Vateva/esp32-c3-digital-dice/include/welcome_bitmap.h

#ifndef WELCOME_BITMAP_H
#define WELCOME_BITMAP_H

#include <pgmspace.h>
// 'welcome_image_dice', 128x16px
const unsigned char welcome_image_dice[] PROGMEM = {
	0x00, 0x00, 0x00, 0x00, 0x00, 0x00, 0x00, 0x00, 0x00, 0x00, 0x00, 0x00, 0x00, 0x00, 0x00, 0x00, 
	0x1f, 0xfe, 0x00, 0x7f, 0xf8, 0x01, 0xff, 0xe0, 0x07, 0xff, 0x80, 0x1f, 0xfe, 0x00, 0x7f, 0xf8, 
	0x3f, 0xff, 0x00, 0xff, 0xfc, 0x03, 0xff, 0xf0, 0x0f, 0xff, 0xc0, 0x3f, 0xff, 0x00, 0xff, 0xfc, 
	0x3f, 0xff, 0x00, 0xff, 0xfc, 0x03, 0xff, 0xf0, 0x0f, 0xff, 0xc0, 0x3f, 0xff, 0x00, 0xff, 0xfc, 
	0x3f, 0xff, 0x00, 0xe7, 0xfc, 0x03, 0x9f, 0xf0, 0x0e, 0x79, 0xc0, 0x39, 0xe7, 0x00, 0xe7, 0x9c, 
	0x3f, 0xff, 0x00, 0xe7, 0xfc, 0x03, 0x9f, 0xf0, 0x0e, 0x79, 0xc0, 0x39, 0xe7, 0x00, 0xe7, 0x9c, 
	0x3f, 0xff, 0x00, 0xff, 0xfc, 0x03, 0xff, 0xf0, 0x0f, 0xff, 0xc0, 0x3f, 0xff, 0x00, 0xff, 0xfc, 
	0x3f, 0x3f, 0x00, 0xff, 0xfc, 0x03, 0xf3, 0xf0, 0x0f, 0xff, 0xc0, 0x3f, 0x3f, 0x00, 0xe7, 0x9c, 
	0x3f, 0x3f, 0x00, 0xff, 0xfc, 0x03, 0xf3, 0xf0, 0x0f, 0xff, 0xc0, 0x3f, 0x3f, 0x00, 0xe7, 0x9c, 
	0x3f, 0xff, 0x00, 0xff, 0xfc, 0x03, 0xff, 0xf0, 0x0f, 0xff, 0xc0, 0x3f, 0xff, 0x00, 0xff, 0xfc, 
	0x3f, 0xff, 0x00, 0xff, 0x9c, 0x03, 0xfe, 0x70, 0x0e, 0x79, 0xc0, 0x39, 0xe7, 0x00, 0xe7, 0x9c, 
	0x3f, 0xff, 0x00, 0xff, 0x9c, 0x03, 0xfe, 0x70, 0x0e, 0x79, 0xc0, 0x39, 0xe7, 0x00, 0xe7, 0x9c, 
	0x3f, 0xff, 0x00, 0xff, 0xfc, 0x03, 0xff, 0xf0, 0x0f, 0xff, 0xc0, 0x3f, 0xff, 0x00, 0xff, 0xfc, 
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
	greyhound0,
	greyhound1,
	greyhound2
};
// Array of all bitmaps for convenience. (Total bytes used to store images in PROGMEM = 272)
const int welcome_image_dice_allArray_LEN = 1;
const unsigned char* welcome_image_dice_allArray[1] = {
	welcome_image_dice
};


#endif
