Vateva/esp32-c3-digital-dice/include/d10_bitmaps_32.h

#ifndef D10_BITMAPS_32_H
#define D10_BITMAPS_32_H

#include <pgmspace.h>
// 'd10_32_0', 32x32px
const unsigned char d10_32_0 [] PROGMEM = {
	0x00, 0x00, 0x00, 0x00, 0x00, 0x00, 0x00, 0x00, 0x00, 0x00, 0x00, 0x00, 0x00, 0x00, 0x00, 0x00, 
	0x00, 0x00, 0x00, 0x00, 0x00, 0x03, 0x00, 0x00, 0x00, 0x02, 0xf0, 0x00, 0x00, 0x00, 0x0c, 0x00, 
	0x00, 0x00, 0x07, 0x00, 0x00, 0x03, 0xff, 0xc0, 0x00, 0x07, 0xff, 0xc0, 0x00, 0x3f, 0xff, 0xc0, 
	0x00, 0x7f, 0xff, 0xe0, 0x03, 0xff, 0xff, 0xe0, 0x0f, 0xff, 0xff, 0xf0, 0x0f, 0xff, 0xff, 0xf0, 
	0x0f, 0xff, 0xff, 0xf0, 0x0f, 0xff, 0xff, 0xf0, 0x07, 0xff, 0xff, 0xe0, 0x07, 0xff, 0xff, 0xe0, 
	0x07, 0xff, 0xff, 0xc0, 0x07, 0xff, 0xff, 0xc0, 0x03, 0xff, 0xff, 0x80, 0x01, 0xff, 0xff, 0x00, 
	0x00, 0x7f, 0xfe, 0x00, 0x00, 0x1f, 0xf8, 0x00, 0x00, 0x03, 0x70, 0x00, 0x00, 0x00, 0x00, 0x00, 
	0x00, 0x00, 0x00, 0x00, 0x00, 0x00, 0x00, 0x00, 0x00, 0x00, 0x00, 0x00, 0x00, 0x00, 0x00, 0x00
};
// 'd10_32_1', 32x32px
const unsigned char d10_32_1 [] PROGMEM = {
	0x00, 0x00, 0x00, 0x00, 0x00, 0x00, 0x00, 0x00, 0x00, 0x00, 0x00, 0x00, 0x00, 0x00, 0x00, 0x00, 
	0x00, 0x01, 0xc0, 0x00, 0x00, 0x3f, 0xf0, 0x00, 0x00, 0x7f, 0xf8, 0x00, 0x00, 0xff, 0xfe, 0x00, 
	0x01, 0xff, 0xff, 0x00, 0x03, 0xff, 0xff, 0x00, 0x01, 0xff, 0xff, 0x80, 0x02, 0x3f, 0xff, 0xc0, 
	0x02, 0x03, 0xff, 0xc0, 0x02, 0x00, 0x6f, 0xc0, 0x02, 0x00, 0xe0, 0x00, 0x02, 0x01, 0xe0, 0x40, 
	0x02, 0x03, 0xe0, 0x40, 0x02, 0x07, 0xf0, 0x80, 0x01, 0x0f, 0xf0, 0x80, 0x01, 0x1f, 0xf0, 0x80, 
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
	d10_32_8__4_,
	d10_32_8__5_,
	d10_32_8__6_,
	d10_32_8__7_,

	d10_32_9__1_,
	d10_32_9__2_,
	d10_32_9__3_,
	d10_32_9__4_,
	d10_32_9__5_,
	d10_32_9__6_,
	d10_32_9__7_,

    d10_32_10__1_,
	d10_32_10__2_,
	d10_32_10__3_,
	d10_32_10__4_,
	d10_32_10__5_,
	d10_32_10__6_,
	d10_32_10__7_
};

#endif
