Vateva/esp32-c3-digital-dice/include/d12_bitmaps_32.h

#ifndef D12_BITMAPS_32_H
#define D12_BITMAPS_32_H

#include <pgmspace.h>
// 'd12_32', 32x32px
const unsigned char d12_32 [] PROGMEM = {
	0x00, 0x00, 0x00, 0x00, 0x00, 0x00, 0x00, 0x00, 0x00, 0x00, 0x00, 0x00, 0x00, 0x00, 0x00, 0x00, 
	0x00, 0x00, 0x00, 0x00, 0x00, 0x0f, 0xf0, 0x00, 0x00, 0x1f, 0xf8, 0x00, 0x00, 0x3f, 0xfc, 0x00, 
	0x00, 0x3f, 0xfe, 0x00, 0x00, 0x3f, 0xff, 0x00, 0x00, 0x7f, 0xff, 0x80, 0x00, 0xff, 0xff, 0x80, 
	0x01, 0xff, 0xff, 0x80, 0x03, 0xff, 0xff, 0xc0, 0x07, 0xff, 0xff, 0xc0, 0x07, 0xff, 0xff, 0xc0, 
	0x07, 0xff, 0xff, 0xc0, 0x07, 0xff, 0xff, 0xc0, 0x03, 0xff, 0xff, 0xc0, 0x03, 0xff, 0xff, 0xc0, 
	0x03, 0xff, 0xff, 0x80, 0x01, 0xff, 0xff, 0x80, 0x01, 0xff, 0xff, 0x00, 0x00, 0xe7, 0xfe, 0x00, 
	0x00, 0x01, 0xfc, 0x00, 0x00, 0x00, 0x3c, 0x00, 0x00, 0x00, 0x00, 0x00, 0x00, 0x00, 0x00, 0x00, 
	0x00, 0x00, 0x00, 0x00, 0x00, 0x00, 0x00, 0x00, 0x00, 0x00, 0x00, 0x00, 0x00, 0x00, 0x00, 0x00
};
// 'd12_32_1 (1)', 32x32px
const unsigned char d12_32_1__1_ [] PROGMEM = {
	0x00, 0x00, 0x00, 0x00, 0x00, 0x00, 0x00, 0x00, 0x00, 0x00, 0x00, 0x00, 0x00, 0x00, 0x00, 0x00, 
	0x00, 0x03, 0x00, 0x00, 0x00, 0x07, 0xe0, 0x00, 0x00, 0x3f, 0xf8, 0x00, 0x00, 0xff, 0xfc, 0x00, 
	0x00, 0x7f, 0xfe, 0x00, 0x00, 0x3f, 0xff, 0x00, 0x00, 0x1f, 0xff, 0x80, 0x00, 0x1f, 0xff, 0x80, 
	0x02, 0x19, 0xff, 0xc0, 0x00, 0x98, 0xff, 0xc0, 0x00, 0x38, 0x7f, 0xc0, 0x06, 0xb8, 0x3f, 0xc0, 
	0x01, 0x39, 0x13, 0xc0, 0x00, 0x39, 0x83, 0x80, 0x00, 0x3f, 0xc7, 0x00, 0x00, 0x3f, 0x8c, 0x00, 
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
	d12_32_6__3_,
	d12_32_6__4_,
	d12_32_6__5_,
	d12_32_6__6_,
	d12_32_6__7_,

	d12_32_7__1_,
	d12_32_7__2_,
	d12_32_7__3_,
	d12_32_7__4_,
	d12_32_7__5_,
	d12_32_7__6_,
	d12_32_7__7_,

	d12_32_8__1_,
	d12_32_8__2_,
	d12_32_8__3_,
	d12_32_8__4_,
	d12_32_8__5_,
	d12_32_8__6_,
	d12_32_8__7_,
	

	d12_32_9__1_,
	d12_32_9__2_,
	d12_32_9__3_,
	d12_32_9__4_,
	d12_32_9__5_,
	d12_32_9__6_,
	d12_32_9__7_,

	d12_32_10__1_,
	d12_32_10__2_,
	d12_32_10__3_,
	d12_32_10__4_,
	d12_32_10__5_,
	d12_32_10__6_,
	d12_32_10__7_,

	d12_32_11__1_,
	d12_32_11__2_,
	d12_32_11__3_,
	d12_32_11__4_,
	d12_32_11__5_,
	d12_32_11__6_,
	d12_32_11__7_,

	d12_32_12__1_,
	d12_32_12__2_,
	d12_32_12__3_,
	d12_32_12__4_,
	d12_32_12__5_,
	d12_32_12__6_,
	d12_32_12__7_
	
};


#endif
