Vateva/esp32-c3-digital-dice/include/d20_bitmaps_32.h

#ifndef D20_BITMAPS_32_H
#define D20_BITMAPS_32_H

#include <pgmspace.h>
// 'D20_1_11_32 (7)', 32x32px
const unsigned char d20_32_1_7_ [] PROGMEM = {
	0x00, 0x00, 0x00, 0x00, 0x00, 0x00, 0x00, 0x00, 0x00, 0x00, 0x00, 0x00, 0x00, 0x00, 0x00, 0x00, 
	0x00, 0x00, 0xf0, 0x00, 0x00, 0xff, 0xf8, 0x00, 0x00, 0xf7, 0xfc, 0x00, 0x00, 0x83, 0xfe, 0x00, 
	0x01, 0xa7, 0xff, 0x00, 0x01, 0xcf, 0x1f, 0x00, 0x01, 0xdf, 0x0f, 0xc0, 0x01, 0xff, 0x07, 0xe0, 
	0x01, 0xff, 0x23, 0xf0, 0x01, 0xff, 0x31, 0xf8, 0x01, 0xff, 0x38, 0xf8, 0x01, 0xff, 0x3c, 0x70, 
	0x01, 0xff, 0xfe, 0x60, 0x00, 0xff, 0xff, 0xc0, 0x00, 0xff, 0xff, 0x20, 0x02, 0xff, 0xff, 0x80, 
	0x00, 0xe0, 0xfe, 0x40, 0x00, 0xf5, 0xf8, 0x40, 0x00, 0x3c, 0xe0, 0x00, 0x00, 0x3f, 0xc0, 0x00, 
	0x00, 0x3f, 0x80, 0x00, 0x00, 0x1e, 0x00, 0x00, 0x00, 0x1c, 0x00, 0x00, 0x00, 0x00, 0x00, 0x00, 
	0x00, 0x00, 0x00, 0x00, 0x00, 0x00, 0x00, 0x00, 0x00, 0x00, 0x00, 0x00, 0x00, 0x00, 0x00, 0x00
};
// 'D20_1_11_32 (2)', 32x32px
const unsigned char d20_32_1_2_ [] PROGMEM = {
	0x00, 0x00, 0x00, 0x00, 0x00, 0x00, 0x00, 0x00, 0x00, 0x00, 0x00, 0x00, 0x00, 0x00, 0x00, 0x00, 
	0x00, 0x00, 0xf0, 0x00, 0x00, 0xff, 0xf8, 0x00, 0x00, 0xfb, 0xfc, 0x00, 0x00, 0x23, 0xfe, 0x00, 
	0x01, 0x83, 0xff, 0x80, 0x01, 0xcf, 0x1f, 0x00, 0x01, 0xff, 0x0f, 0xc0, 0x03, 0xff, 0x07, 0xe0, 
	0x03, 0xff, 0x23, 0xf0, 0x03, 0xff, 0x31, 0xf8, 0x07, 0xff, 0x38, 0xf8, 0x0f, 0xff, 0x3c, 0x70, 
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
};
// 'D20_10_11_32 (3)', 32x32px
const unsigned char d20_32_10_3_ [] PROGMEM = {
	0x00, 0x00, 0x00, 0x00, 0x00, 0x00, 0x00, 0x00, 0x00, 0x00, 0x00, 0x00, 0x00, 0x00, 0x00, 0x00, 
	0x00, 0x0c, 0x00, 0x00, 0x00, 0x3f, 0xf8, 0x00, 0x00, 0x7f, 0xff, 0x00, 0x00, 0xfb, 0xff, 0x00, 
	0x00, 0x63, 0xff, 0x80, 0x00, 0x6f, 0xff, 0xc0, 0x00, 0xff, 0x07, 0x40, 0x00, 0xff, 0x33, 0xe0, 
	0x00, 0xff, 0x31, 0xf0, 0x00, 0xf9, 0x18, 0xf8, 0x00, 0xf8, 0x8c, 0x78, 0x00, 0xf8, 0x46, 0x7c, 
	0x00, 0xf8, 0x22, 0x78, 0x00, 0xf9, 0x10, 0x78, 0x00, 0x79, 0x88, 0xf0, 0x00, 0x7f, 0xc7, 0x90, 
	0x01, 0x7f, 0xe7, 0xa0, 0x00, 0x7c, 0xfc, 0x40, 0x00, 0xf9, 0xf8, 0x00, 0x00, 0x3b, 0xe0, 0x00, 
	0x00, 0x3f, 0x80, 0x00, 0x00, 0x3e, 0x00, 0x00, 0x00, 0x18, 0x00, 0x00, 0x00, 0x00, 0x00, 0x00, 
	0x00, 0x00, 0x00, 0x00, 0x00, 0x00, 0x00, 0x00, 0x00, 0x00, 0x00, 0x00, 0x00, 0x00, 0x00, 0x00
};
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
